jonsag/ardAudioCenter/ardAudioCenter-PIO/src/chars.h

/*******************************
   Custom characters
 *******************************/

/*******************************
   Volume and balance bar
 *******************************/
const byte bar1[8] = {
    0b10000,
    0b10000,
    0b10000,
    0b11111,
    0b10000,
    0b10000,
    0b10000,
    0b00000};

const byte bar2[8] = {
    0b01000,
    0b01000,
    0b01000,
    0b11111,
    0b01000,
    0b01000,
    0b01000,
    0b00000};

const byte bar3[8] = {
    0b00100,
    0b00100,
    0b00100,
    0b11111,
    0b00100,
    0b00100,
    0b00100,
    0b00000};

const byte bar4[8] = {
    0b00010,
    0b00010,
    0b00010,
    0b11111,
    0b00010,
    0b00010,
    0b00010,
    0b00000};

const byte bar5[8] = {
    0b00001,
    0b00001,
    0b00001,
    0b11111,
    0b00001,
    0b00001,
    0b00001,
    0b00000};

/*
byte fill1[8] = {
  0b10000,
  0b10000,
  0b10000,
  0b10000,
  0b10000,
  0b10000,
  0b10000,
  0b00000
};

byte fill2[8] = {
  0b11000,
  0b11000,
  0b11000,
  0b11000,
  0b11000,
  0b11000,
  0b11000,
  0b00000
};

byte fill3[8] = {
  0b11100,
  0b11100,
  0b11100,
  0b11100,
  0b11100,
  0b11100,
  0b11100,
  0b00000
};

byte fill4[8] = {
  0b11110,
  0b11110,
  0b11110,
  0b11110,
  0b11110,
  0b11110,
  0b11110,
  0b00000
};

byte fill5[8] = {
  0b11111,
  0b11111,
  0b11111,
  0b11111,
  0b11111,
  0b11111,
  0b11111,
  0b00000
}
*/
