jonsag/ardAudioCenter/ardAudioCenter-PIO/src/volume.h

void writeVolumes()
{
  debugMess("Volume left: ");
  debugMessln(volL);
  debugMess("Volume right: ");
  debugMessln(volR);
  debugMessln();

  digitalWrite(csPL, LOW); // set volume for left channel
  SPI.transfer(B00010001); // tell the chip to set the pot
  SPI.transfer(volL);      // set pot position
  digitalWrite(csPL, HIGH);

  digitalWrite(csPR, LOW); // set volume for right channel
  SPI.transfer(B00010001); // tell the chip to set the pot
  SPI.transfer(volR);      // set pot position
  digitalWrite(csPR, HIGH);
}

void setVolume()
{
  volumeVal = 255 * volume / 100;

  debugMess("Volume value: ");
  debugMessln(volumeVal);
  debugMessln();

  if (balance < 10) // shift sound center to the left
  {
    volR = volumeVal * balance / 10;
  }
  else
  {
    volR = volumeVal;
  }

  if (balance > 10) // shift sound center to the right
  {
    volL = volumeVal * (20 - balance) / 10;
  }
  else
  {
    volL = volumeVal;
  }

  writeVolumes();
}
